SP5GW/EMI_Filter_Analysis/sim/EMC_Filter_Analysis.asc

C1: cap; {Cx}
C2: cap; {Cy}
C3: cap; {Cy}
C4: cap; {Cx}
C5: cap; {Cx}
C6: cap; {Cx}
C7: cap; {Cy}
C8: cap; {Cy}
C9: cap; {Cx}
C10: cap; {Cx}
C11: cap; {Cx}
C12: cap; {Cy}
C13: cap; {Cy}
C14: cap; {Cx}
C15: cap; {Cx}
C16: cap; {Cx}
C17: cap; {Cy}
C18: cap; {Cy}
C19: cap; {Cx}
C20: cap; {Cx}
L1: ind2; {L}
L2: ind2; {L}
L3: ind; 3µ
L4: ind; 3µ
L5: ind2; {L}
L6: ind2; {L}
L7: ind2; {L}
L8: ind2; {L}
L9: ind; 3µ
L10: ind; 3µ
L11: ind2; {L}
L12: ind2; {L}
L13: ind2; {L}
L14: ind2; {L}
L15: ind; 3µ
L16: ind; 3µ
L17: ind2; {L}
L18: ind2; {L}
L19: ind2; {L}
L20: ind2; {L}
L21: ind; 3µ
L22: ind; 3µ
L23: ind2; {L}
L24: ind2; {L}
R1: res; 50
R2: res; 0.001
R3: res; 0.001
R4: res; 50
R5: res; 0.001
R6: res; 50
R7: res; 0.001
R8: res; 0.001
R9: res; 50
R10: res; 0.001
V1: signal; AC 1; Rser=50
V2: signal; AC 1; Rser=50
V3: signal; AC 1; Rser=50
V4: signal; AC 1; Rser=50
Named nets: 0, Out_diff, In_diff, Out_com, In_com, Out_diff_rev, In_diff_rev, Out_com_rev, In_com_rev
.param Cx=220n
.param Cy=2.2n
.param L=0.7m
Differential Mode Measurement
.tran 50ms
k1 L5 L6 0.95
k2 L1 L2 0.95
.ac dec 100 10k 50Meg
Common Mode Measurement
k3 L11 L12 0.95
k4 L7 L8 0.95
Differential Mode Measurement - Reversed Connection
k5 L17 L18 0.95
k6 L13 L14 0.95
Common Mode Measurement - Reversed Connection
k7 L23 L24 0.95
k8 L19 L20 0.95
